roge-rm/sugarshieldXL/pictures/2.jpg

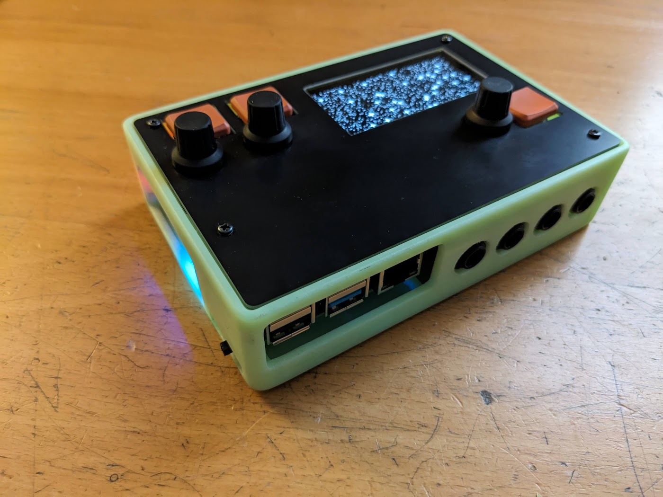
pictures/2.jpg
